dipa-cotton/static/production/cart image files/cart5.png

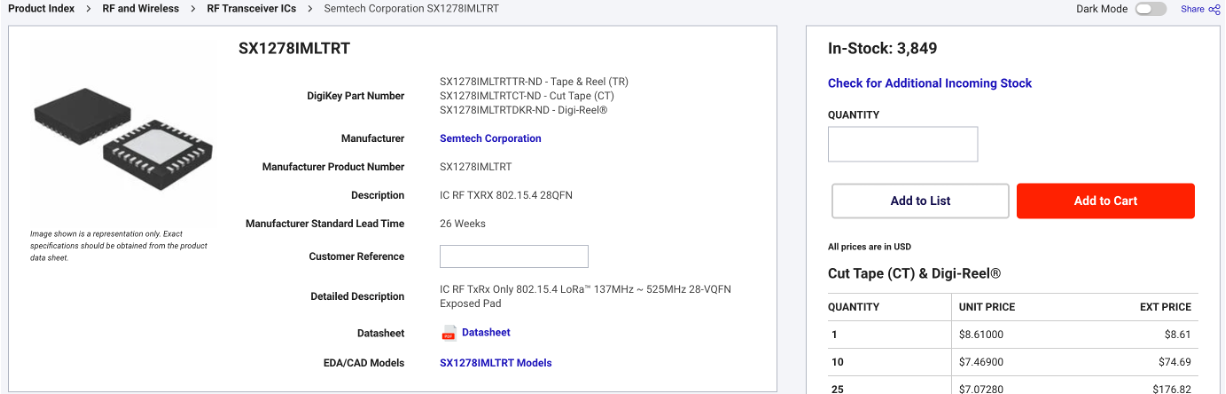
production/cart image files/cart5.png
